ldes89150/Monolithic-Cavity-Design-ECDL/GR13-1208-Solidworks.sldprt

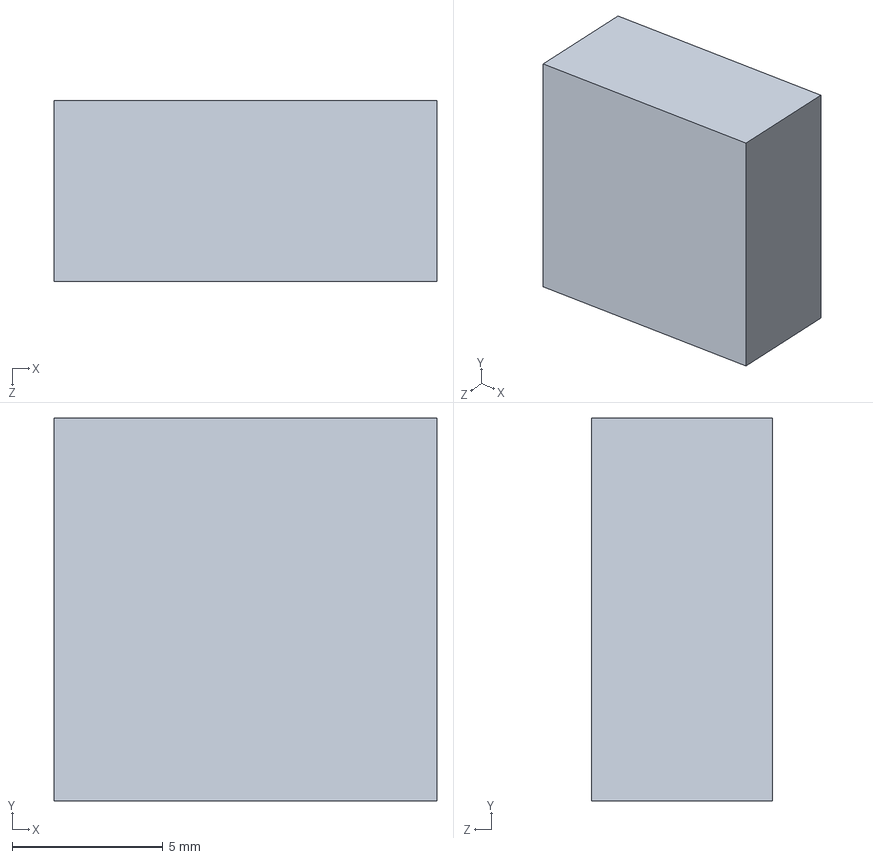
[picture p40: CAD file, 2015-08-17]
GR13-1208-Solidworks.sldprt
12.7 x 12.7 x 6.00 mm
