ldes89150/Monolithic-Cavity-Design-ECDL/arm part1.SLDPRT

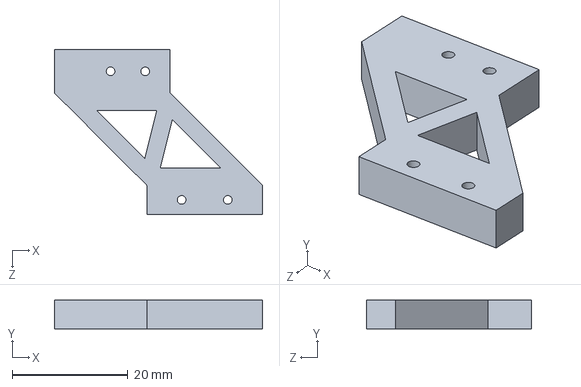
[picture p41: CAD file, 2015-08-17]
arm part1.SLDPRT
36.0 x 5.00 x 28.5 mm
