ldes89150/Monolithic-Cavity-Design-ECDL/laser1.SLDPRT

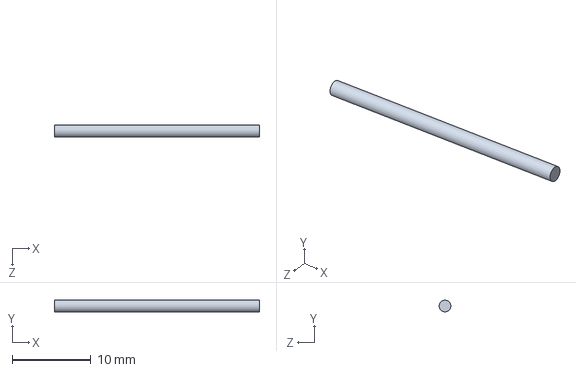
[picture p42: CAD file, 2015-08-17]
laser1.SLDPRT
26.0 x 1.50 x 1.50 mm
