ldes89150/Monolithic-Cavity-Design-ECDL/top.SLDPRT

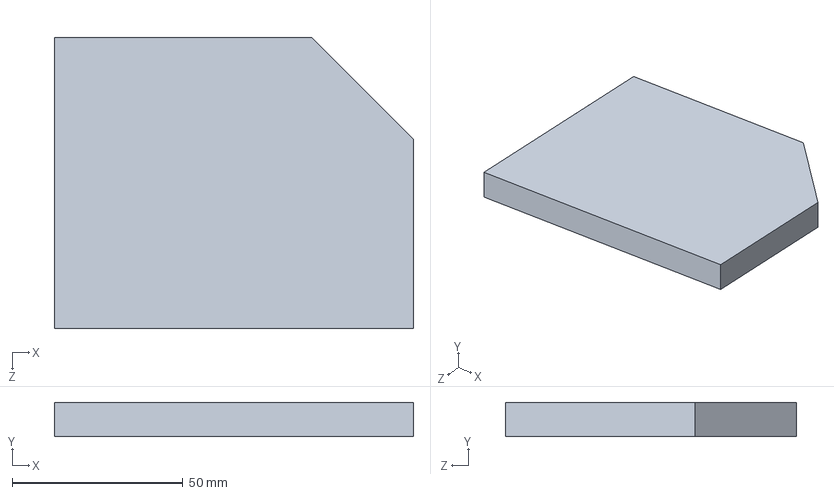
[picture p43: CAD file, 2015-08-17]
top.SLDPRT
105.0 x 10.0 x 85.0 mm
