ldes89150/Monolithic-Cavity-Design-ECDL/BB05-E03-Solidworks.sldprt

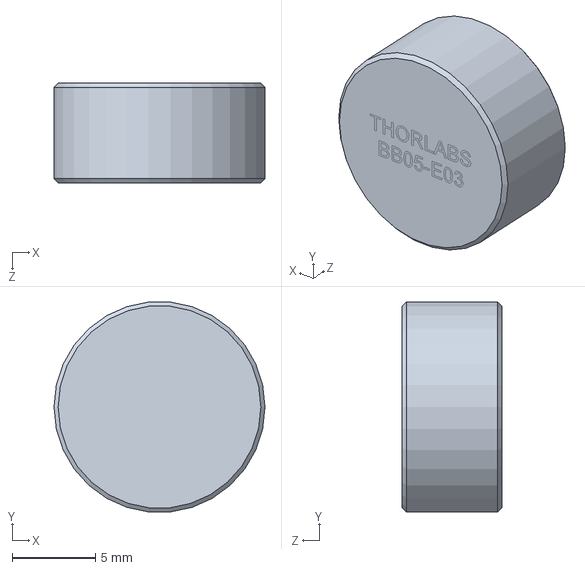
[picture p44: CAD file, 2015-08-17]
BB05-E03-Solidworks.sldprt
12.7 x 12.6 x 6.00 mm
