ldes89150/Monolithic-Cavity-Design-ECDL/colimation tube final ver2.SLDPRT

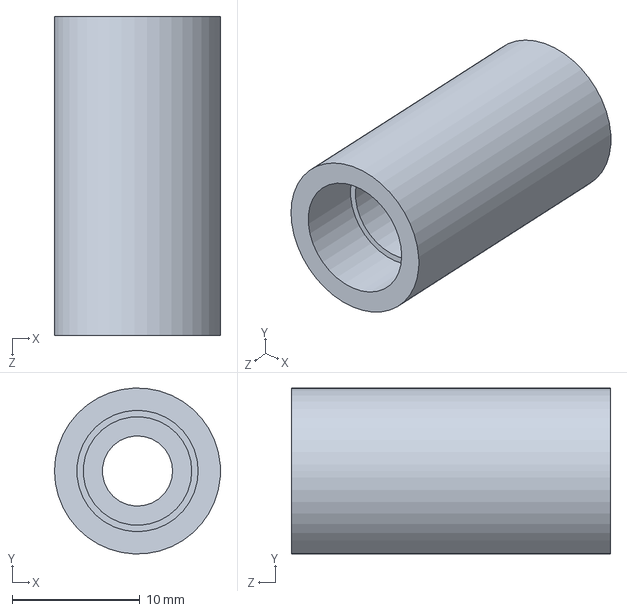
[picture p45: CAD file, 2015-08-17]
colimation tube final ver2.SLDPRT
13.0 x 13.0 x 25.0 mm
